megasaturnv/arduino-gps-tracker/maps/Step4 Export As.png

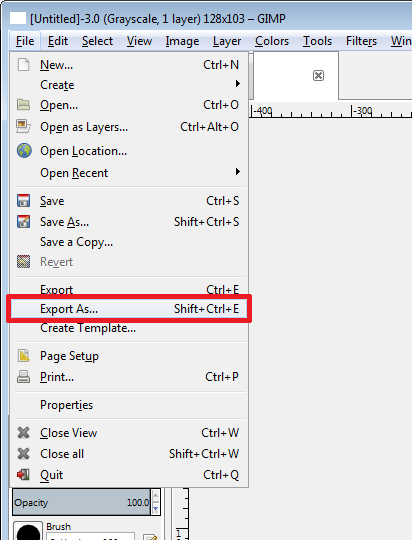
maps/Step4 Export As.png
