megasaturnv/arduino-gps-tracker/maps/Step5 Export Settings.png

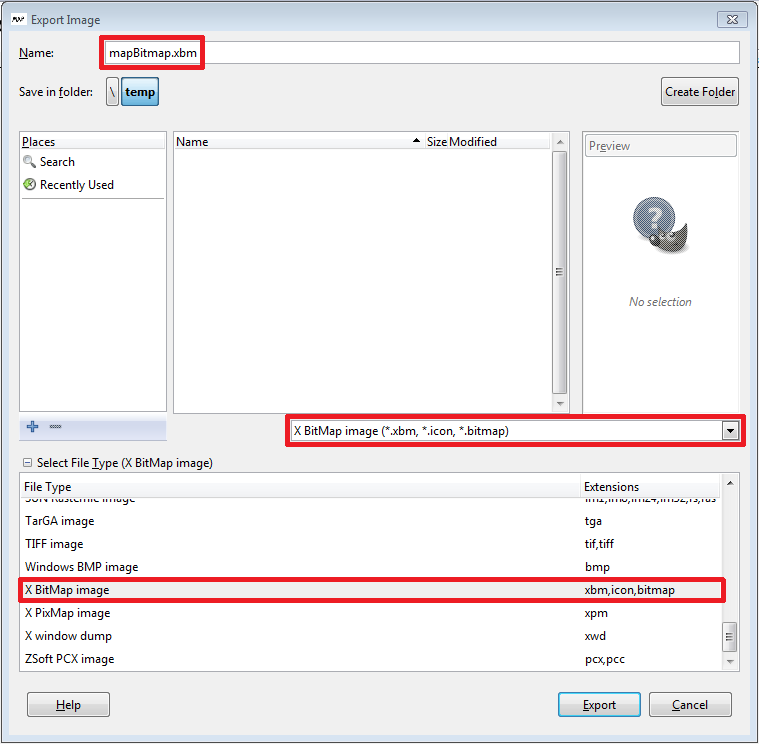
maps/Step5 Export Settings.png
