megasaturnv/arduino-gps-tracker/handheldController/mapBitmap.h

static const uint8_t mapBitmap[] PROGMEM = {
  0x00, 0x00, 0x00, 0x00, 0x00, 0x00, 0x06, 0x00, 0x10, 0x00, 0x00, 0x00,
  0x02, 0x08, 0x00, 0x00, 0x00, 0x00, 0x00, 0x00, 0x00, 0x80, 0x01, 0x00,
  0x0c, 0x00, 0x00, 0x00, 0x02, 0x04, 0x00, 0x00, 0x00, 0x00, 0x00, 0x00,
  0x00, 0x60, 0x00, 0x00, 0x02, 0x00, 0x00, 0x00, 0x02, 0x02, 0x00, 0x00,
  0x00, 0x00, 0x00, 0x00, 0x00, 0x10, 0x00, 0x80, 0x01, 0x00, 0x00, 0x00,
  0x02, 0x02, 0x00, 0x00, 0x00, 0x00, 0x00, 0x00, 0x00, 0x0c, 0x00, 0x40,
  0x00, 0x00, 0x00, 0x00, 0x02, 0x01, 0x00, 0x00, 0x00, 0x00, 0x00, 0x00,
  0x80, 0x03, 0x00, 0x30, 0x00, 0x00, 0x00, 0x00, 0x82, 0x00, 0x00, 0x00,
  0x00, 0x00, 0x00, 0x00, 0x40, 0x00, 0x00, 0x08, 0x00, 0x00, 0x00, 0x00,
  0x43, 0x00, 0x00, 0x80, 0x00, 0x00, 0x00, 0x00, 0x30, 0x00, 0x00, 0x06,
  0x00, 0x00, 0x00, 0x00, 0x41, 0x00, 0x00, 0x40, 0x00, 0x00, 0x00, 0x00,
  0x0c, 0x00, 0x00, 0x01, 0x00, 0x00, 0x00, 0x00, 0x21, 0x00, 0x00, 0x20,
  0x00, 0x00, 0x00, 0x00, 0x02, 0x00, 0xc0, 0x00, 0x00, 0x00, 0x00, 0x00,
  0x11, 0x00, 0x00, 0x10, 0x00, 0x00, 0x00, 0xc0, 0x01, 0x00, 0x30, 0x00,
  0x00, 0x00, 0x00, 0x00, 0x09, 0x00, 0x00, 0x08, 0x00, 0x00, 0x00, 0x30,
  0x00, 0x00, 0x08, 0x00, 0x00, 0x00, 0x00, 0x00, 0x09, 0x00, 0x00, 0x84,
  0x00, 0x00, 0x00, 0x08, 0x00, 0x00, 0x06, 0x00, 0x00, 0x00, 0x00, 0x00,
  0x05, 0x00, 0x00, 0x42, 0x00, 0x00, 0x00, 0x04, 0x00, 0x80, 0x03, 0x00,
  0x00, 0x00, 0x00, 0x80, 0x02, 0x00, 0x00, 0x21, 0x00, 0x00, 0x00, 0x03,
  0x00, 0x60, 0x00, 0x00, 0x00, 0x00, 0x00, 0xe0, 0x01, 0x00, 0x80, 0x10,
  0x00, 0x00, 0xc0, 0x04, 0x00, 0x10, 0x00, 0x00, 0x00, 0x00, 0x00, 0x10,
  0x01, 0x00, 0x40, 0x10, 0x00, 0x00, 0x20, 0x04, 0x00, 0x0c, 0x00, 0x00,
  0x00, 0x00, 0x00, 0x1f, 0x01, 0x00, 0x40, 0x08, 0x00, 0x00, 0x18, 0x04,
  0x00, 0x06, 0x00, 0x00, 0x00, 0x00, 0xfc, 0x18, 0x03, 0x00, 0x20, 0x04,
  0x00, 0x00, 0x06, 0x04, 0x00, 0x02, 0x00, 0x00, 0x00, 0xc0, 0x07, 0x90,
  0x1d, 0x00, 0x20, 0x02, 0x00, 0x80, 0x01, 0x08, 0x00, 0x04, 0x00, 0x00,
  0x00, 0x78, 0x00, 0xec, 0xe0, 0x00, 0x10, 0x02, 0x00, 0x00, 0x00, 0x08,
  0x00, 0x04, 0x00, 0x00, 0x00, 0x06, 0x00, 0x42, 0x00, 0x07, 0x10, 0x01,
  0x00, 0x60, 0x00, 0x10, 0x00, 0x0c, 0x00, 0x00, 0x80, 0x01, 0x80, 0x41,
  0x00, 0x38, 0x08, 0x01, 0x00, 0x18, 0x00, 0x10, 0x00, 0x08, 0x00, 0x00,
  0xe0, 0x00, 0x40, 0x40, 0x00, 0xc0, 0x89, 0x00, 0x00, 0x04, 0x00, 0x20,
  0x00, 0x10, 0x00, 0x00, 0x20, 0x00, 0x20, 0x40, 0x00, 0x00, 0x86, 0x00,
  0x00, 0x02, 0x00, 0x60, 0x00, 0x20, 0x00, 0x00, 0x18, 0x00, 0x18, 0x80,
  0x00, 0x00, 0x44, 0x00, 0x80, 0x01, 0x00, 0x40, 0x00, 0x20, 0x00, 0x00,
  0x0c, 0x00, 0x04, 0x80, 0x00, 0x00, 0x42, 0x00, 0x40, 0x00, 0x00, 0x40,
  0x00, 0x20, 0x00, 0x00, 0x03, 0x00, 0x02, 0x80, 0x00, 0x00, 0x22, 0x00,
  0x38, 0x00, 0x00, 0x80, 0x00, 0x10, 0x00, 0x80, 0x01, 0x00, 0x01, 0x80,
  0x00, 0x00, 0x21, 0x00, 0x04, 0x00, 0x00, 0x00, 0x01, 0x1c, 0x00, 0x40,
  0x00, 0xc0, 0x00, 0x80, 0x00, 0x00, 0x11, 0x00, 0x03, 0x00, 0x00, 0x00,
  0x01, 0x07, 0x00, 0x38, 0x00, 0x20, 0x00, 0x80, 0x00, 0x80, 0x10, 0x00,
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
};
